bkw777/GenBox/img/BaffleBox_half_wall_anchor_2.jpg

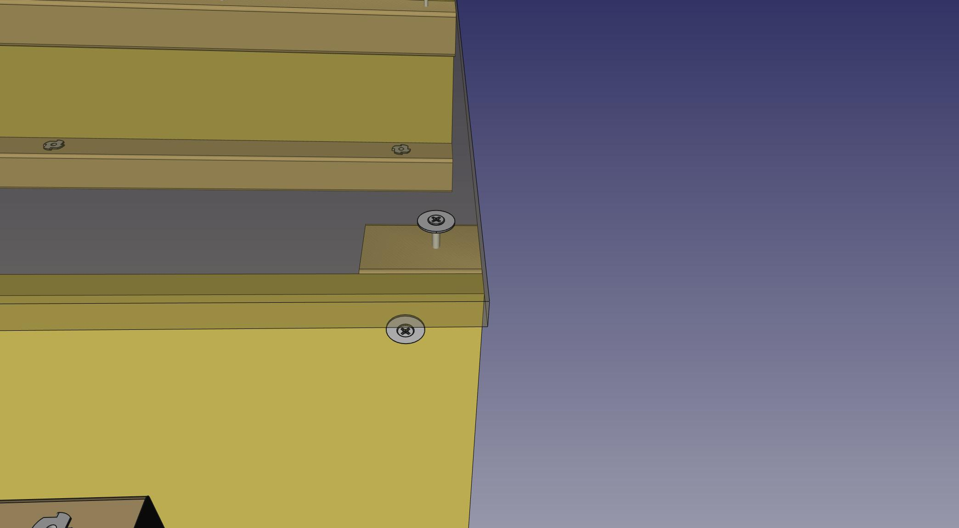
img/BaffleBox_half_wall_anchor_2.jpg
