bkw777/GenBox/img/BaffleBox_half_wall_anchor_3.jpg

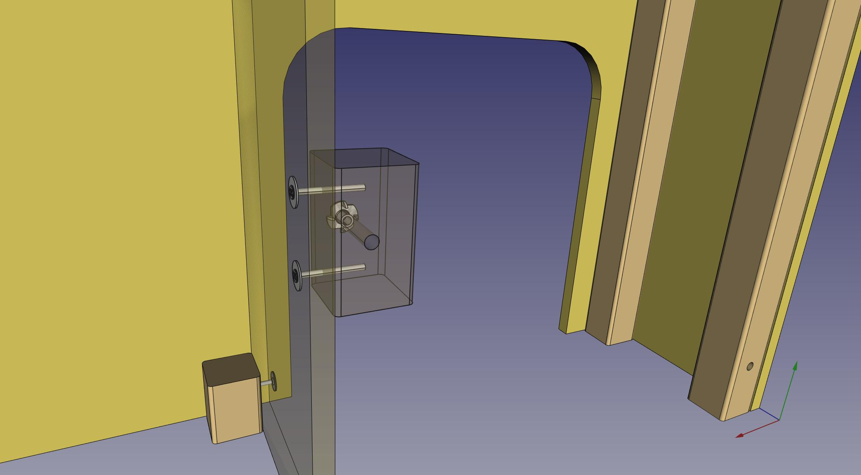
img/BaffleBox_half_wall_anchor_3.jpg
