bkw777/GenBox/img/GenBox_1.jpg

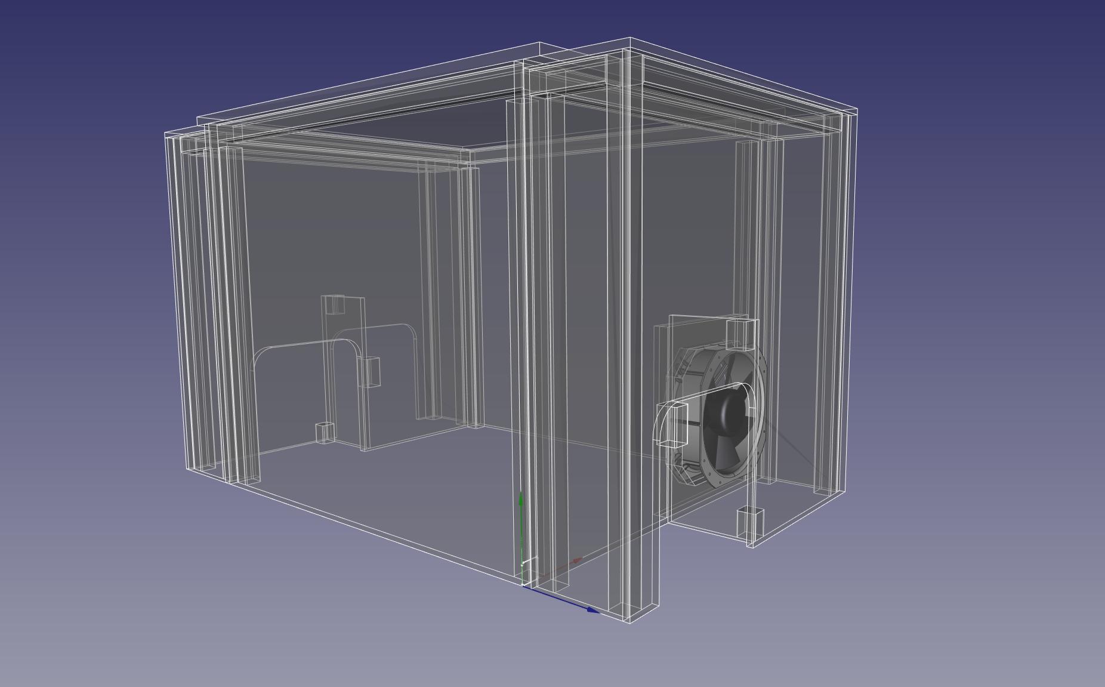
img/GenBox_1.jpg
