bkw777/GenBox/img/GenBox_2.jpg

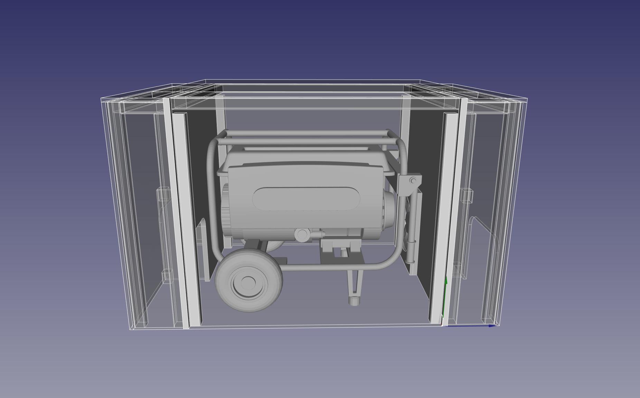
img/GenBox_2.jpg
