bkw777/GenBox/img/GenBox_3.jpg

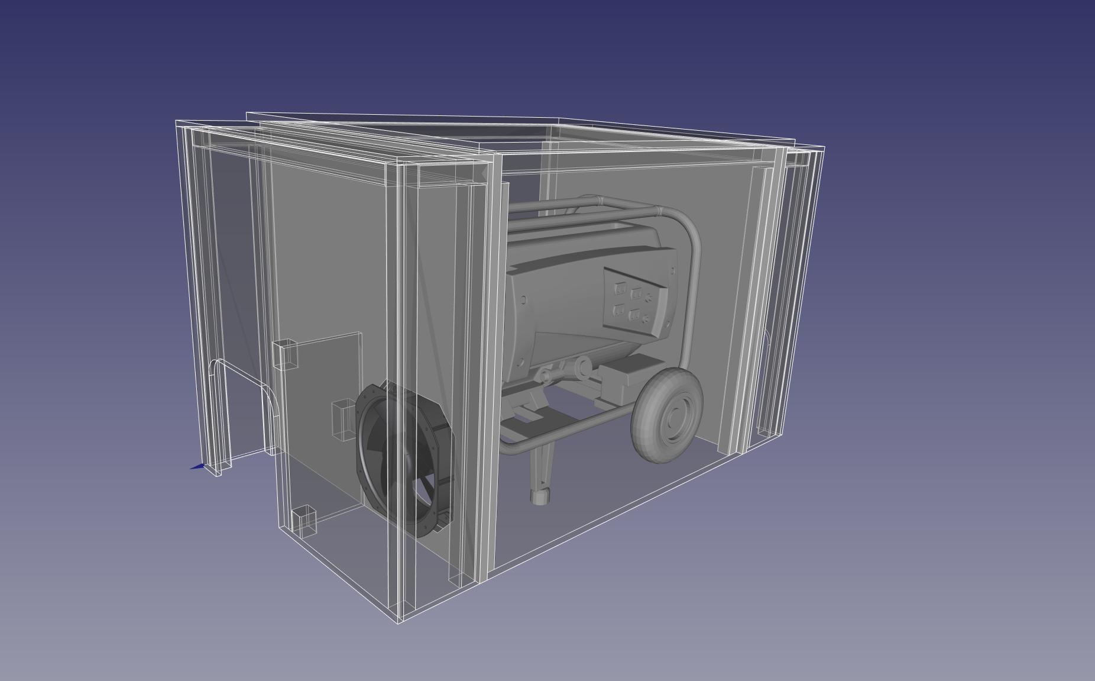
img/GenBox_3.jpg
