bkw777/GenBox/img/GenBox_4.jpg

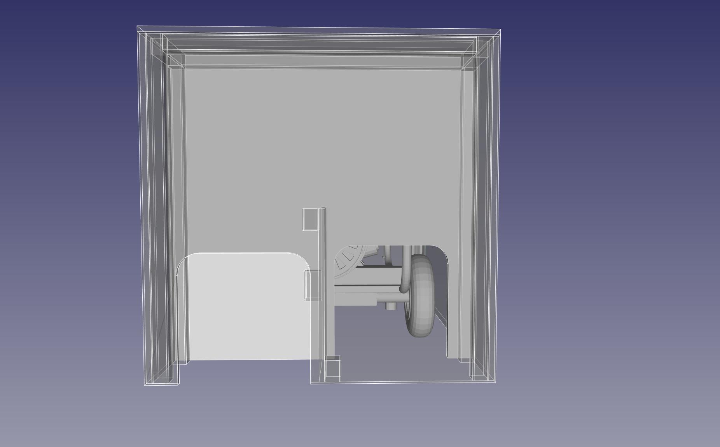
img/GenBox_4.jpg
