bkw777/GenBox/img/GenBox_6.jpg

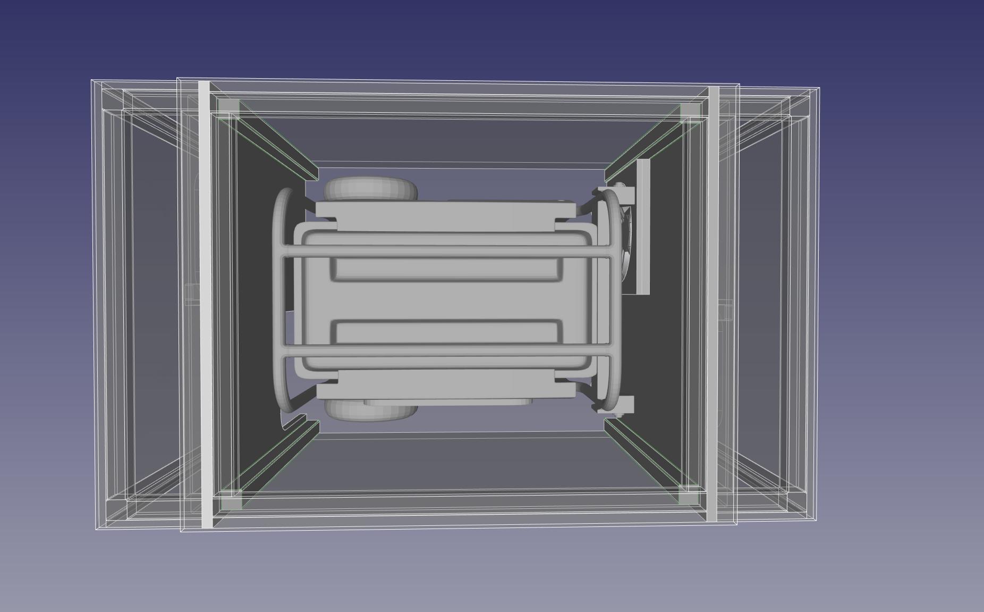
img/GenBox_6.jpg
