bkw777/GenBox/img/Inlet_Box_1.jpg

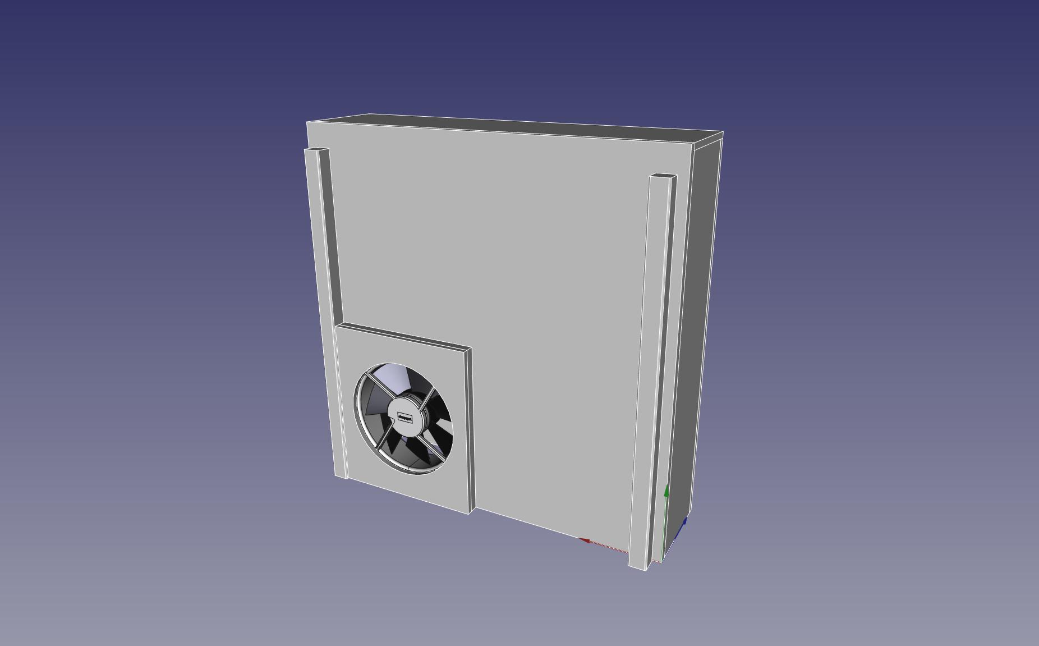
img/Inlet_Box_1.jpg
