bkw777/GenBox/img/Inlet_Box_2.jpg

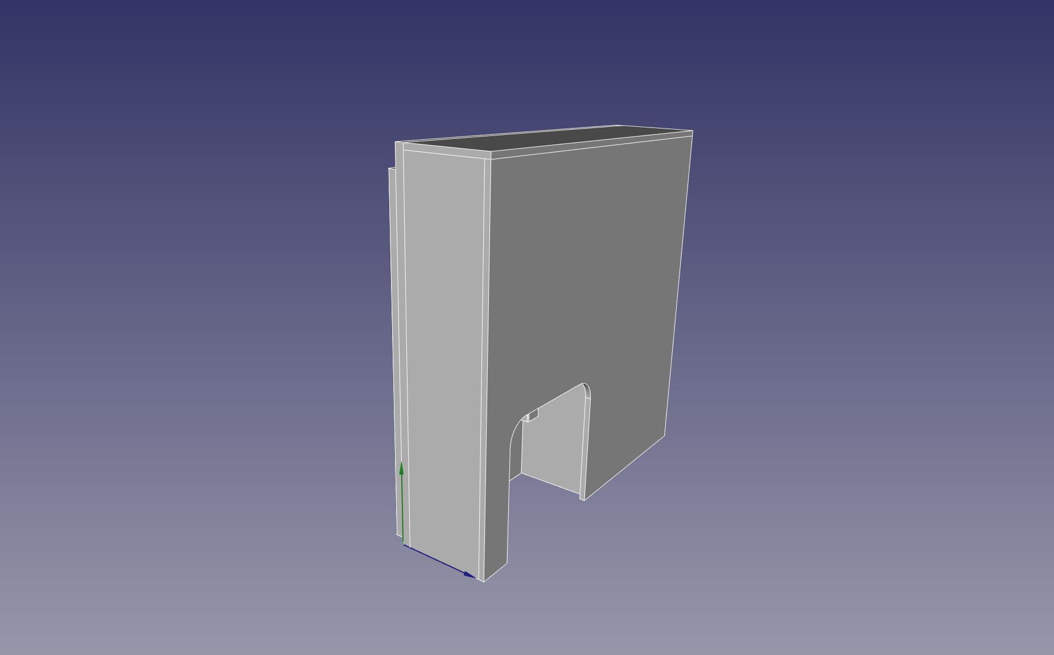
img/Inlet_Box_2.jpg
