bkw777/GenBox/img/Inlet_Box_3.jpg

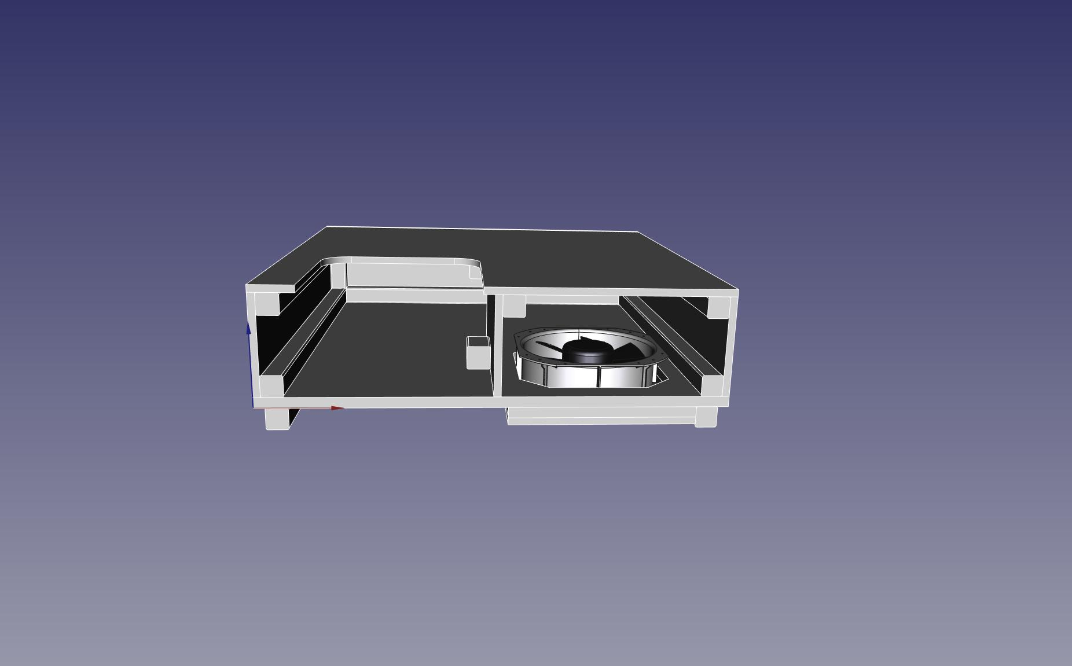
img/Inlet_Box_3.jpg
